eGuardianDev/SmartClock/src/main/Wifi.hpp

#ifndef _WIFI_hpp__
#define _WIFI_hpp__
// #include <Arduino_JSON.h>

#include "Logger.hpp"

const int MAXATTEMPTSTOCONNECTWIFI = 15;

Preferences SettingsEEPROM;

#define RW_MODE false
#define RO_MODE true

bool setupWifi() {
  
  // Define a custom configuration
  WiFiProvisioner::Config customCfg(
      "Alarm Configuration",   // Access Point Name
      "Welcome to WiFi configuration", // HTML Page Title
      "#0989d8",                     // Theme Color
      R"rawliteral(<svg id="Icons" xmlns="http://www.w3.org/2000/svg" width="5rem" height="5rem" viewBox="0 0 512 512"><defs><style>.cls-3{fill:#6b250c}.cls-4{fill:#7a2b13}.cls-5{fill:#dd8c29}.cls-6{fill:#efb732}.cls-7{fill:#962a11}.cls-8{fill:#f9eaa5}.cls-9{fill:#fad98f}.cls-10{fill:#f39e22}.cls-11{fill:#f9c744}.cls-12{fill:#c44a1a}.cls-13{fill:#decee5}.cls-14{fill:#f4e6f4}.cls-16{fill:#fff}.cls-17{fill:#2e3140}.cls-18{fill:#334353}.cls-20{fill:#ccfdff}</style></defs><circle cx="256" cy="256" r="255.98" style="fill:#0989d8"/><path d="M0 255.76A255.63 255.63 0 0 1 103.44 50.44c113.54-84.25 273.87-60.52 358.12 53a254.76 254.76 0 0 1 49.93 136 76.89 76.89 0 0 0-14.24 6.88c-23.84 14.74-42 41.9-69.91 44.44-19.15 1.75-37.29-9.24-51.1-22.62s-24.87-29.51-39.4-42.12a112.53 112.53 0 0 0-157.7 10c-14.17 15.89-26.53 37.44-47.68 40-28.75 3.44-51.22-31.63-80-28.95-9.3.87-17.72 5.66-26.73 8a54.5 54.5 0 0 1-24.73.69z" style="fill:#29a3fb"/><path class="cls-3" d="M269.55 125.29 220 211.15a12.09 12.09 0 0 1-16.51 4.43L168 195.09a12.1 12.1 0 0 1-4.43-16.52l49.58-85.86A16.57 16.57 0 0 1 232 85a8.47 8.47 0 0 0 9.37-3.53l24-36.76-.29-.17a3.66 3.66 0 0 1-.84-5.68l7.44-7.95a3.66 3.66 0 0 1 4.51-.68l16 9.25a3.68 3.68 0 0 1 1.68 4.25l-3.17 10.41a3.67 3.67 0 0 1-5.35 2.11l-.29-.16-19.9 39.17a8.43 8.43 0 0 0 1.63 9.88 16.57 16.57 0 0 1 2.76 20.15z"/><path class="cls-4" d="M269.55 125.29 220 211.15a12.09 12.09 0 0 1-16.51 4.43l-25.62-14.79a12.1 12.1 0 0 1-4.42-16.52l47.7-82.62a12.47 12.47 0 0 1 17-4.57 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
cls-17" d="M237.45 231.24v7.15a7 7 0 0 0 7 7h7.15a7 7 0 0 0 7-7v-7.15a5.91 5.91 0 0 0 0-.6 7 7 0 0 0-6.94-6.36h-7.15a7 7 0 0 0-6.93 6.36 5.88 5.88 0 0 0-.13.6z"/><path class="cls-20" d="M194.39 155h19.1a7 7 0 0 1 7 7v10.59h-33.13V162a7 7 0 0 1 7.03-7z"/><path class="cls-16" d="m142.08 172.63 20-20a10.53 10.53 0 0 1 14.9 0l20 20zM212.41 172.63l15.26-15.26a8 8 0 0 1 11.36 0l15.26 15.26z"/><path class="cls-20" d="M283.8 149.51h33a8.73 8.73 0 0 1 8.73 8.73v14.39h-50.47v-14.39a8.73 8.73 0 0 1 8.74-8.73z"/><path class="cls-16" d="m314 172.63 15.27-15.26a8 8 0 0 1 11.35 0l15.27 15.26z"/></svg>)rawliteral", // SVG Logo
      "Alarm config", // Project Title
      "Setup the wifi system",       // Project Sub-title
      "Connection to WiFi to access weather and other updates",
                                     // Project Information
      "Current page displayed thanks to © Custom WiFiProvisioner"
      "System created by eGuardian Development. https://eguardian.dev", // Footer
                                                      // Text
      "The device is now connected to WiFi.", // Success Message
      "This action will erase all stored settings", // Reset Confirmation Text
      "API Key",  // Input Field Text
      4,          // Input Field Length
      false,       // Show Input Field
      true        // Show Reset Field
  );

  // Create the WiFiProvisioner instance with the custom configuration
  WiFiProvisioner provisioner(customCfg);

  // Set up callbacks
  provisioner.onProvision([]() { Serial.println("Provisioning started."); })
      .onInputCheck([](const char *input) -> bool {
        // Serial.printf("Checking if input code equals to 1234: %s\n", input);
        return strcmp(input, "1234") == 0; // Validate input
      })
      .onSuccess([](const char *ssid, const char *password, const char *input) {

        SettingsEEPROM.begin("wifiSettings", RW_MODE);

        logger.debug(String("Connected to SSID: ") + ssid);
        SettingsEEPROM.putString("SSID_Name",String(ssid));
        if (password) {
          SettingsEEPROM.putString("SSID_Pass",String(password));
          logger.debug(String("Password: ") + password);
        }else{
          SettingsEEPROM.putString("SSID_Pass",String(""));
        }

        
        SettingsEEPROM.end();
        logger.debug("[ Settings ] saved!");
        
        if (input) {
          // logger.debug("Input: %s\n", input);
        }
        logger.log("Provisioning completed successfully!");
      })
      .onFactoryReset([]() { logger.warning("Factory reset triggered!"); 
      });

  // Start provisioning

  SettingsEEPROM.begin("wifiSettings", RO_MODE);  

  bool wifiAccount = SettingsEEPROM.isKey("SSID_Name");

  if(!wifiAccount){
    SettingsEEPROM.end();
    SettingsEEPROM.begin("wifiSettings", RW_MODE);  
    provisioner.startProvisioning();
  }else{
    String wifiName = SettingsEEPROM.getString("SSID_Name");
    String wifiPass = SettingsEEPROM.getString("SSID_Pass");
    SettingsEEPROM.end();
    logger.debug(String("wifi is: ")+ wifiName);
    logger.debug(String("wifi password is: ")+ wifiPass);
    
    if(wifiName == ""){
      logger.error("Empty wifi name. Starting Provisioning");
      provisioner.startProvisioning();
    }

    WiFi.begin(wifiName, wifiPass);
    logger.log(" [ Wifi ] Connecting");
    printText(String("Connecting to Wifi..."));

    int count = 0;
    while(WiFi.status() != WL_CONNECTED && count <MAXATTEMPTSTOCONNECTWIFI) {
      delay(500);
      logger.debug(String("attempting... ") + String(count));
      count++;
    } 

    if(count>=MAXATTEMPTSTOCONNECTWIFI){
      logger.log("Connection timeout. Entering discovery mode.");
      printText(String("No wifi, entering setup..."));
      provisioner.startProvisioning();
      delay(500);
    }else{
      logger.log("Connection established");
      printText(String("All done!"));
      delay(500);
    }

    return true;
  }
}

bool checkWifiConnection(){
  return (WiFi.status() == WL_CONNECTED);
}

bool setup_mDNS(){
  return MDNS.begin("alarm-clock");
}

#endif //_WIFI_hpp__
